bobbaddeley/F20_Respirator/images/attached_front.jpg

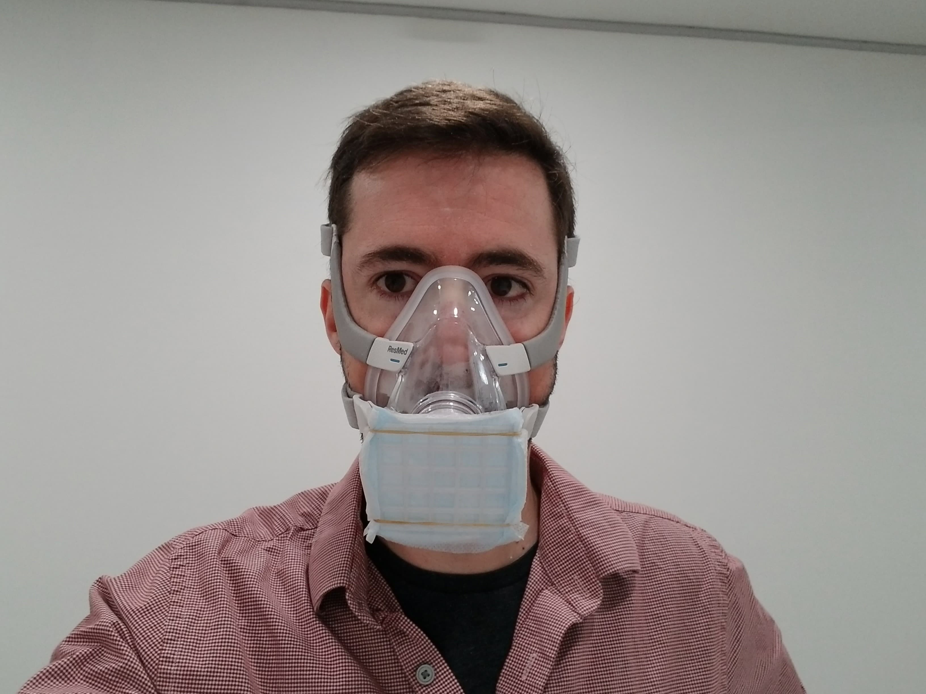
images/attached_front.jpg
