bobbaddeley/F20_Respirator/images/funnel_back.jpg

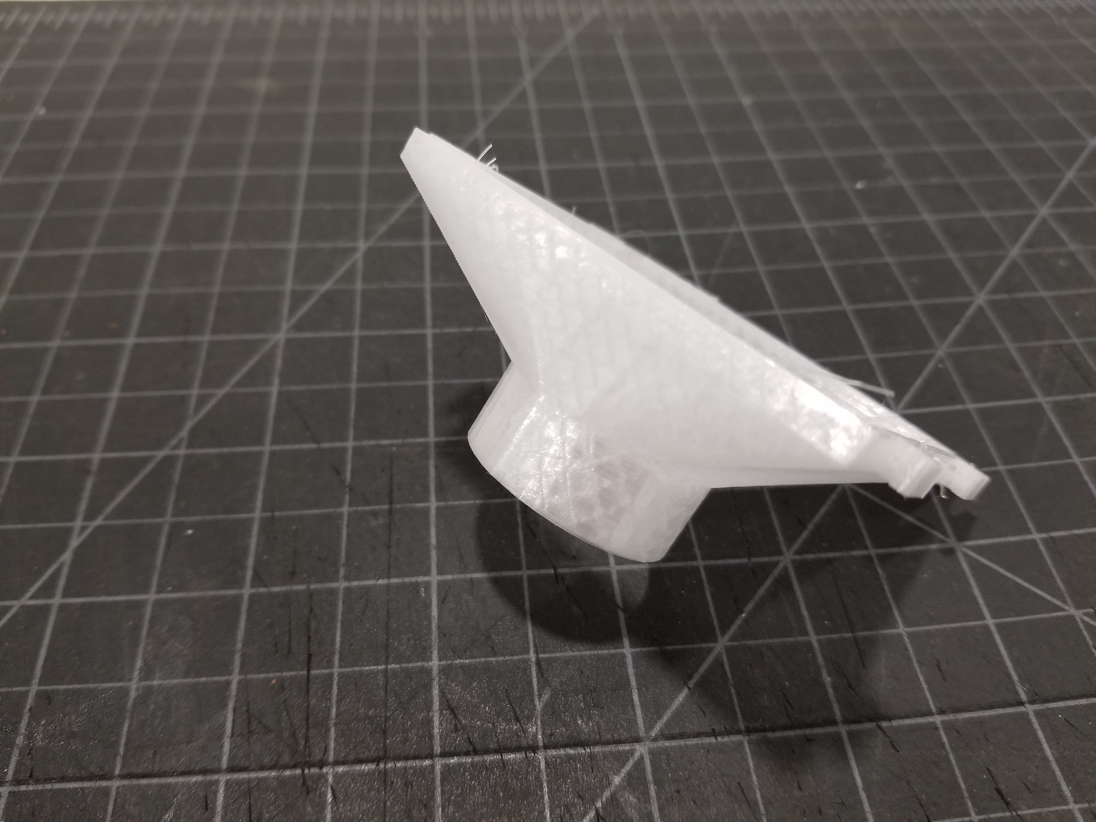
images/funnel_back.jpg
