bobbaddeley/F20_Respirator/images/Grill.JPG

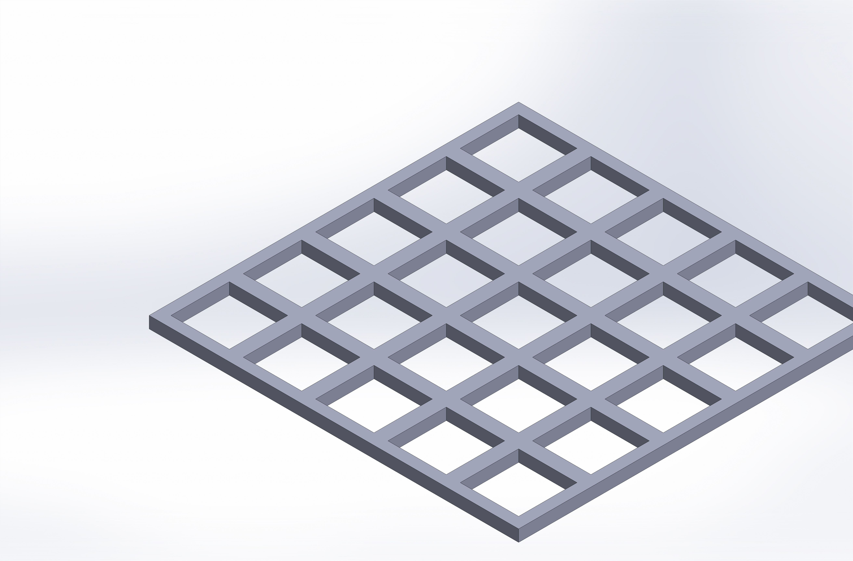
images/Grill.JPG
