bobbaddeley/F20_Respirator/port/F20_AirInletPort.JPG

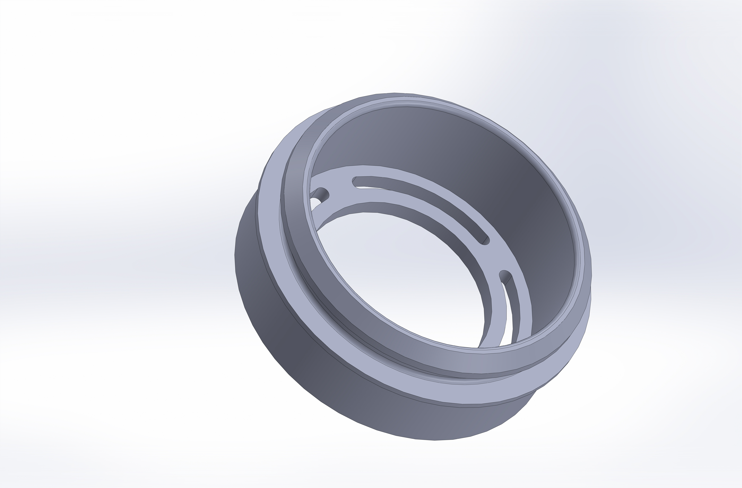
port/F20_AirInletPort.JPG
