bobbaddeley/F20_Respirator/port/F20_AirInletPort_Side.JPG

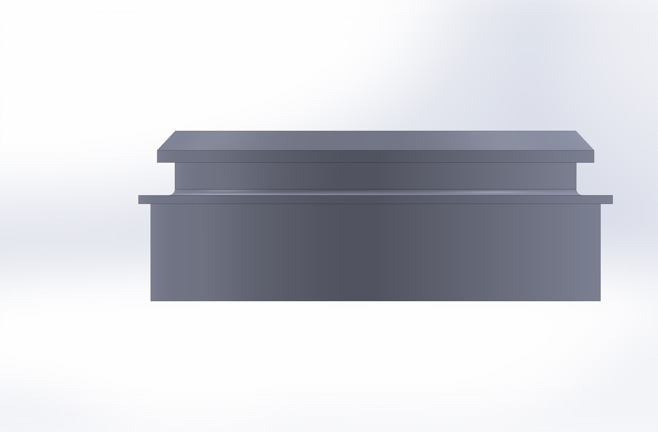
port/F20_AirInletPort_Side.JPG
