bobbaddeley/F20_Respirator/images/assembled_no_rubber.jpg

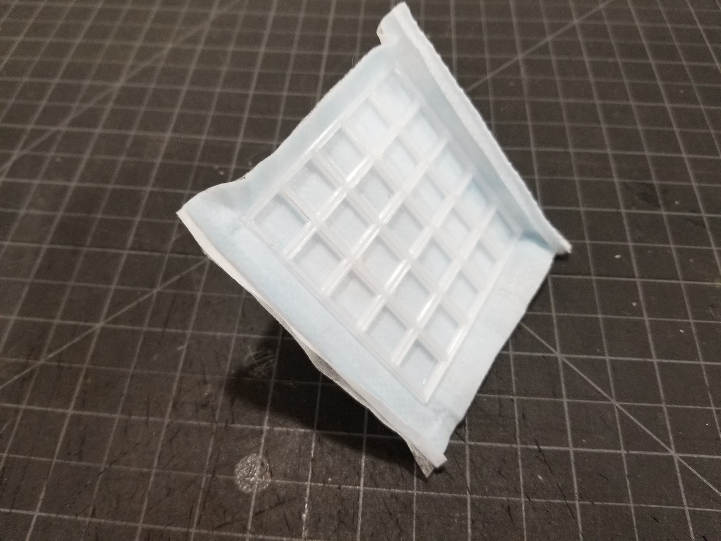
images/assembled_no_rubber.jpg
