bobbaddeley/F20_Respirator/images/assembled_rubber.jpg

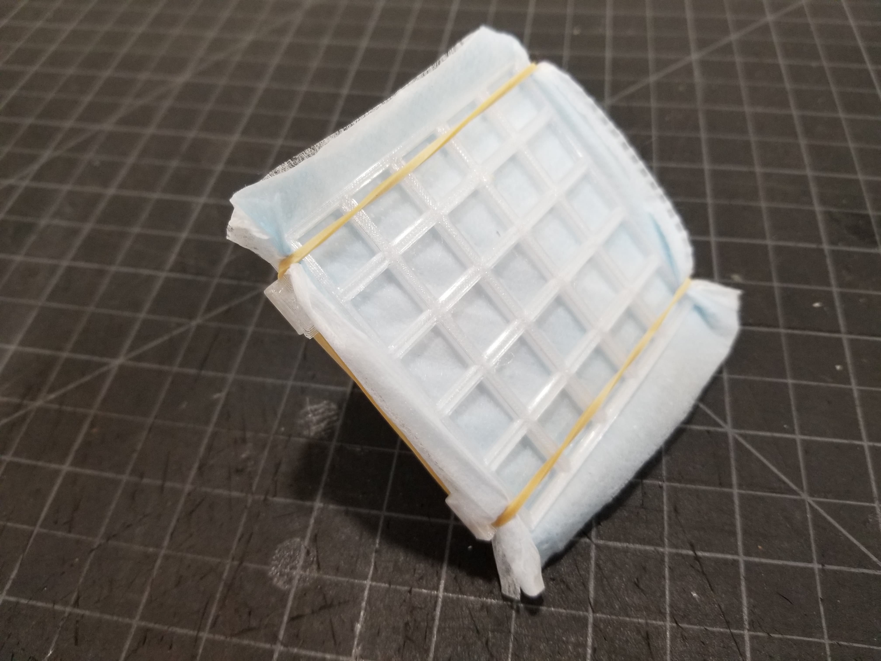
images/assembled_rubber.jpg
