bobbaddeley/F20_Respirator/images/assembled_side.jpg

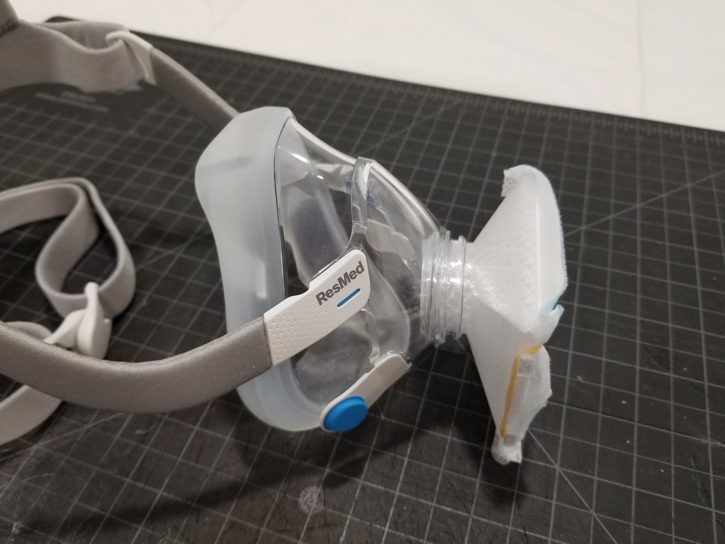
images/assembled_side.jpg
